koppchen/serge-tkb-led-mod/ltspice/serge-tkb-leds-cd4051b.asc

AND1: and
AND2: and
AND3: and
AND4: and
D1: LED
D2: LED
D3: LED
D4: LED
INV1: inv
INV2: inv
R1: res; 4.99k
R2: res; 1.2k
V1: signal; PULSE(0 12 0.5 5u 5u 0.5 1)
V2: signal; PULSE(0 12 1 5u 5u 1 2)
V3: voltage; 12
Named nets: A, B, Row1, Row2, Row3, Row4, 0
.tran 0 4S
Serge TKB row LED mod
CD4051B
